DrNicoleTobias/Ray_PaperArtifacts/Review_Material/ITW_Data_Samples/W1_HW1_Summary.png

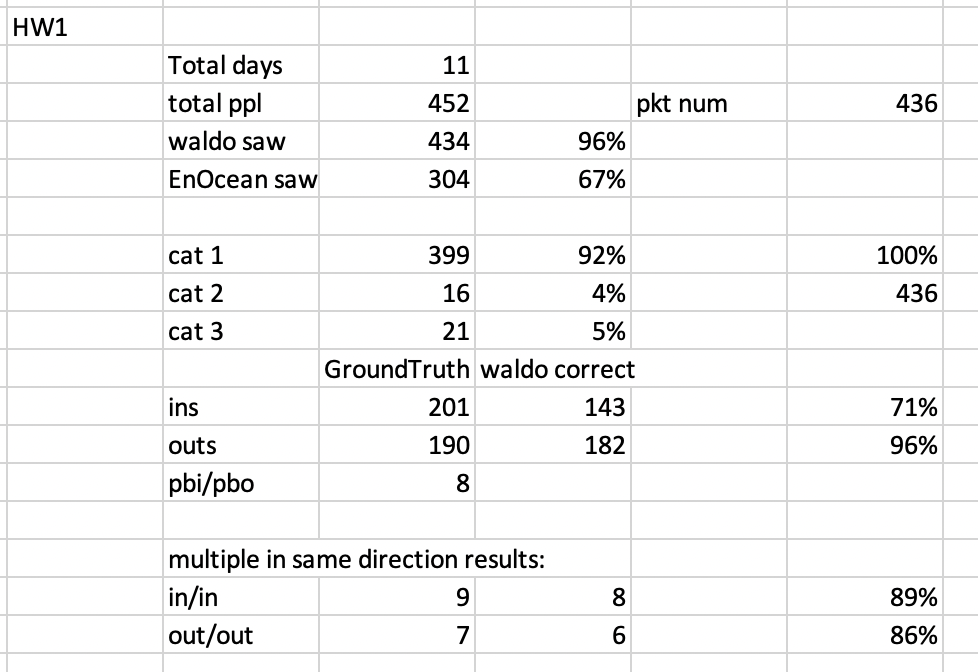
Review_Material/ITW_Data_Samples/W1_HW1_Summary.png
