DrNicoleTobias/Ray_PaperArtifacts/Review_Material/ITW_Data_Samples/W5_GT_All_preHW2_Results.xlsx

Date/Time | Location | GT People Count/event | Category | Ground Truth Label | Description of ground truth if not simple in/out event | Sensor and GT agree | Multiple people same direction results | Waldo/Ray Classifiation | Detect ppl/event | EnOcean Detection
2023-01-10 17:02 | preHW2 | 1 | 1 | out |  | out |  | out | 1 | hit | preHW2
2023-01-10 17:30 | preHW2 | 2 | 2 | in/in | two people come in one after another, about 4 seconds |  | in | in | 1 | hit |  | Total days | 11
2023-01-10 17:46 | preHW2 | 4 | 2 | in/in | four people walk in one after another after another, about 8 seconds |  | in | in | 1 | hit |  | total ppl | 1637 |  | pkt num | 1295
2023-01-10 17:56 | preHW2 | 3 | 2 | in/in | 3 people walk in, one then two came in after together, about 7 seconds |  | in | in | 1 | hit |  | waldo saw | 1316 | 80.39095907%
2023-01-10 18:36 | preHW2 | 1 | 1 | out |  | out |  | out | 1 | hit |  | EnOcean saw | 640 | 39.09590715%
2023-01-10 18:37 | preHW2 | 1 | 1 | in |  | in |  | in | 1 | miss
2023-01-10 18:47 | preHW2 | 1 | 1 | out |  | out |  | out | 1 | hit |  | cat 1 | 1100 | 84.94208494% |  | 99.92277992%
2023-01-10 18:48 | preHW2 | 1 | 1 | in |  | in |  | in | 1 | miss |  | cat 2 | 130 | 10.03861004% |  | 1294
2023-01-10 18:48 | preHW2 | 1 | 1 | out |  | out |  | out | 1 | miss |  | cat 3 | 64 | 4.942084942%
2023-01-11 01:55 | preHW2 | 1 | 1 | out |  | out |  | out | 1 | hit |  |  | GroundTruth | waldo correct
2023-01-11 06:48 | preHW2 | 1 | 1 | in |  | in |  | in | 1 | hit |  | ins | 579 | 560 |  | 96.71848014%
2023-01-11 07:16 | preHW2 | 1 | 1 | in |  |  |  | out | 1 | miss |  | outs | 512 | 476 |  | 92.96875%
2023-01-11 07:19 | preHW2 | 1 | 1 | in |  | in |  | in | 1 | hit |  | pbi/pbo | 9 | 6 |  | 66.66666667%
2023-01-11 07:23 | preHW2 | 1 | 1 | in |  | in |  | in | 1 | hit
2023-01-11 07:34 | preHW2 | 1 | 1 | out |  | out |  | out | 1 | hit |  | multiple in same direction results:
2023-01-11 07:37 | preHW2 | 1 | 1 | in |  | in |  | in | 1 | hit |  | in/in | 65 | 56 |  | 86.15384615%
2023-01-11 07:37 | preHW2 | 1 | 1 | out |  | out |  | out | 1 | miss |  | out/out | 65 | 53 |  | 81.53846154%
2023-01-11 07:44 | preHW2 | 1 | 1 | in |  | in |  | in | 1 | hit
2023-01-11 07:48 | preHW2 | 1 | 1 | pbin | lady comes out of her office off camera |  |  | pbo | 1 | hit
2023-01-11 07:52 | preHW2 | 1 | 1 | in |  | in |  | in | 1 | hit
2023-01-11 07:53 | preHW2 | 1 | 1 | out |  | out |  | out | 1 | miss
2023-01-11 08:27 | preHW2 | 1 | 1 | out |  | out |  | out | 1 | hit
2023-01-11 08:36 | preHW2 | 1 | 1 | out |  | out |  | out | 1 | hit
2023-01-11 08:42 | preHW2 | 1 | 1 | in |  | in |  | in | 1 | hit
2023-01-11 08:43 | preHW2 | 1 | 1 | in |  | in |  | in | 1 | miss
2023-01-11 08:44 | preHW2 | 1 | 1 | in |  | in |  | in | 1 | hit
2023-01-11 08:46 | preHW2 | 1 | 1 | in |  | in |  | in | 1 | miss
2023-01-11 08:46 | preHW2 | 1 | 1 | out |  | out |  | out | 1 | hit
2023-01-11 08:49 | preHW2 | 1 | 1 | in |  | in |  | in | 1 | hit
2023-01-11 08:51 | preHW2 | 1 | 1 | in |  | in |  | in | 1 | hit
2023-01-11 08:57 | preHW2 | 1 | 1 | out |  |  |  | pbi | 1 | hit
2023-01-11 08:57 | preHW2 | 1 | 1 | in |  | in |  | in | 1 | miss
2023-01-11 08:57 | preHW2 | 1 | 1 | out |  | out |  | out | 1 | miss
2023-01-11 09:27 | preHW2 | 1 | 1 | in |  | in |  | in | 1 | hit
2023-01-11 09:32 | preHW2 | 1 | 1 | out |  | out |  | out | 1 | hit
2023-01-11 09:34 | preHW2 | 1 | 1 | out |  | out |  | out | 1 | hit
2023-01-11 09:36 | preHW2 | 1 | 1 | in |  | in |  | in | 1 | hit
2023-01-11 09:44 | preHW2 | 1 | 1 | in |  | in |  | in | 1 | hit
2023-01-11 09:52 | preHW2 | 1 | 1 | out |  | out |  | out | 1 | hit
2023-01-11 09:53 | preHW2 | 1 | 1 | in |  | in |  | in | 1 | miss
2023-01-11 09:54 | preHW2 | 1 | 1 | in |  | in |  | in | 1 | miss
2023-01-11 09:56 | preHW2 | 2 | 3 | out/in | two people walk through in different direction in the same event |  |  | in | 1 | hit
2023-01-11 09:57 | preHW2 | 1 | 1 | out |  |  |  | in | 1 | miss
2023-01-11 10:05 | preHW2 | 1 | 1 | out |  | out |  | out | 1 | hit
2023-01-11 10:06 | preHW2 | 1 | 1 | out |  | out |  | out | 1 | miss
2023-01-11 10:09 | preHW2 | 1 | 1 | in |  | in |  | in | 1 | hit
2023-01-11 10:30 | preHW2 | 1 | 1 | out |  | out |  | out | 1 | hit
2023-01-11 10:31 | preHW2 | 1 | 1 | in |  | in |  | in | 1 | miss
2023-01-11 10:33 | preHW2 | 1 | 1 | in |  | in |  | in | 1 | hit
2023-01-11 10:33 | preHW2 | 1 | 1 | out |  | out |  | out | 1 | miss
2023-01-11 10:34 | preHW2 | 1 | 1 | in |  | in |  | in | 1 | miss
2023-01-11 10:37 | preHW2 | 1 | 1 | out |  | out |  | out | 1 | hit
2023-01-11 10:38 | preHW2 | 2 | 2 | out/out | two people walked out together at the same time |  | out | out | 1 | miss
2023-01-11 10:41 | preHW2 | 1 | 1 | in |  | in |  | in | 1 | hit
2023-01-11 10:43 | preHW2 | 1 | 1 | out |  | out |  | out | 1 | hit
2023-01-11 10:50 | preHW2 | 1 | 1 | in |  | in |  | in | 1 | hit
2023-01-11 10:50 | preHW2 | 1 | 1 | in |  | in |  | in | 1 | miss
2023-01-11 10:51 | preHW2 | 1 | 1 | out |  | out |  | out | 1 | miss
2023-01-11 10:52 | preHW2 | 1 | 1 | out |  | out |  | out | 1 | hit
2023-01-11 10:54 | preHW2 | 1 | 1 | in |  | in |  | in | 1 | miss
2023-01-11 11:05 | preHW2 | 1 | 1 | out |  | out |  | out | 1 | hit
2023-01-11 11:05 | preHW2 | 1 | 1 | in |  | in |  | in | 1 | miss
2023-01-11 11:07 | preHW2 | 2 | 3 | out/in | two people walk through in different direction in the same event |  |  | out | 1 | miss
2023-01-11 11:07 | preHW2 | 1 | 1 | in |  | in |  | in | 1 | miss
2023-01-11 11:07 | preHW2 | 1 | 1 | in |  | in |  | in | 1 | miss
2023-01-11 11:08 | preHW2 | 1 | 1 | out |  | out |  | out | 1 | hit
2023-01-11 11:08 | preHW2 | 2 | 2 | in/in | two people walking in after one another with a few seconds in between, this gt lasted about 7 seconds |  |  | in/in | 2 | miss
2023-01-11 11:09 | preHW2 | 1 | 1 | out |  |  |  | in | 1 | miss
2023-01-11 11:10 | preHW2 | 1 | 1 | in |  | in |  | in | 1 | hit
2023-01-11 11:10 | preHW2 | 1 | 1 | out |  | out |  | out | 1 | miss
2023-01-11 11:11 | preHW2 | 1 | 1 | in |  | in |  | in | 1 | miss
2023-01-11 11:11 | preHW2 | 1 | 1 | in |  | in |  | in | 1 | miss
2023-01-11 11:12 | preHW2 | 1 | 1 | in |  | in |  | in | 1 | hit
2023-01-11 11:14 | preHW2 | 1 | 1 | in |  | in |  | in | 1 | miss
2023-01-11 11:27 | preHW2 | 1 | 1 | out |  | out |  | out | 1 | hit
2023-01-11 11:29 | preHW2 | 1 | 1 | in |  | in |  | in | 1 | miss
2023-01-11 11:54 | preHW2 | 1 | 1 | out |  | out |  | out | 1 | hit
2023-01-11 11:54 | preHW2 | 1 | 1 | out |  | out |  | out | 1 | miss
2023-01-11 11:54 | preHW2 | 9 | 2 | out/out | 9 people walk out, class got out, about 18 seconds of walks |  |  | in/pbi | 2 | miss
2023-01-11 11:56 | preHW2 | 1 | 1 | out |  | out |  | out | 1 | hit
2023-01-11 12:03 | preHW2 | 1 | 1 | in |  | in |  | in | 1 | hit
2023-01-11 12:06 | preHW2 | 1 | 1 | pbin | lady comes in of her office off camera | pb |  | pbi | 1 | hit
2023-01-11 12:07 | preHW2 | 1 | 1 | in |  | in |  | in | 1 | miss
2023-01-11 12:08 | preHW2 | 1 | 1 | out |  | out |  | out | 1 | miss
2023-01-11 12:09 | preHW2 | 1 | 1 | in |  | in |  | in | 1 | hit
2023-01-11 12:09 | preHW2 | 2 | 2 | out/out |  |  | out | out | 1 | miss
2023-01-11 12:12 | preHW2 | 1 | 1 | in |  | in |  | in | 1 | hit
2023-01-11 12:13 | preHW2 | 1 | 1 | in | about 6 seconds | in |  | in | 1 | miss
2023-01-11 12:16 | preHW2 | 1 | 1 | in |  | in |  | in | 1 | hit
2023-01-11 12:24 | preHW2 | 1 | 1 | out |  | out |  | out | 1 | hit
2023-01-11 12:35 | preHW2 | 1 | 1 | out |  | out |  | out | 1 | hit
2023-01-11 12:38 | preHW2 | 1 | 1 | out |  | out |  | out | 1 | hit
2023-01-11 12:39 | preHW2 | 1 | 1 | in |  | in |  | in | 1 | miss
2023-01-11 12:39 | preHW2 | 1 | 1 | in |  | in |  | in | 1 | miss
2023-01-11 12:51 | preHW2 | 1 | 1 | out |  | out |  | out | 1 | hit
2023-01-11 12:52 | preHW2 | 2 | 3 | out/in | some one comes in, the other person is going out,, lingers to talk then continues to go out, about 9 seconds |  |  | in | 1 | miss
2023-01-11 12:52 | preHW2 | 1 | 1 | out |  | out |  | out | 1 | miss
2023-01-11 12:58 | preHW2 | 1 | 1 | in |  | in |  | in | 1 | hit
2023-01-11 12:59 | preHW2 | 1 | 1 | out |  | out |  | out | 1 | miss
2023-01-11 13:00 | preHW2 | 1 | 1 | in |  | in |  | in | 1 | miss
2023-01-11 13:00 | preHW2 | 1 | 1 | in |  | in |  | in | 1 | miss
2023-01-11 13:24 | preHW2 | 2 | 2 | in/in | two people walk in slowly together then linger a bit on the pbin side, about 11 seconds |  | in | in | 1 | hit
2023-01-11 13:30 | preHW2 | 2 | 2 | out/out | two people walk out together |  | out | out | 1 | hit
2023-01-11 13:33 | preHW2 | 1 | 1 | in |  | in |  | in | 1 | hit
2023-01-11 13:38 | preHW2 | 1 | 1 | out |  |  |  | in | 1 | hit
2023-01-11 13:40 | preHW2 | 3 | 2 | in/in | one person walks in followed by two walking in together |  | in | in | 1 | hit
2023-01-11 13:47 | preHW2 | 1 | 1 | out |  | out |  | out | 1 | hit
2023-01-11 13:54 | preHW2 | 1 | 1 | in |  | in |  | in | 1 | hit
2023-01-11 13:54 | preHW2 | 1 | 3 | uturn | person starts to go out then switches back in, hard to tell if she crossed the sensor |  |  | in | 1 | miss
2023-01-11 14:03 | preHW2 | 1 | 1 | out |  | out |  | out | 1 | hit
2023-01-11 14:05 | preHW2 | 1 | 1 | in |  | in |  | in | 1 | hit
2023-01-11 14:06 | preHW2 | 1 | 1 | in |  | in |  | in | 1 | miss
2023-01-11 14:08 | preHW2 | 1 | 1 | out |  |  |  | in | 1 | hit
2023-01-11 14:08 | preHW2 | 2 | 3 | out/in | two people walk out in opposite directions |  |  | out | 1 | miss
2023-01-11 14:11 | preHW2 | 3 | 2 | in/in | three, one then two people walkin in with a couple of seconds between |  | in | in | 1 | hit
2023-01-11 14:12 | preHW2 | 1 | 1 | in |  | in |  | in | 1 | miss
2023-01-11 14:14 | preHW2 | 1 | 1 | out |  | out |  | out | 1 | hit
2023-01-11 14:16 | preHW2 | 1 | 1 | in |  | in |  | in | 1 | miss
2023-01-11 14:17 | preHW2 | 2 | 2 | out/out | two people walk out side by side |  | out | out | 1 | hit
2023-01-11 14:20 | preHW2 | 1 | 1 | out |  | out |  | out | 1 | hit
2023-01-11 14:21 | preHW2 | 2 | 2 | in/in | two people walk in side by side |  | in | in | 1 | miss
2023-01-11 14:21 | preHW2 | 1 | 1 | out |  | out |  | out | 1 | miss
2023-01-11 14:22 | preHW2 | 1 | 1 | in |  | in |  | in | 1 | hit
2023-01-11 14:24 | preHW2 | 1 | 1 | in |  | in |  | in | 1 | miss
2023-01-11 14:26 | preHW2 | 1 | 1 | out |  | out |  | out | 1 | hit
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
2023-01-12 10:53 | preHW2 | 1 | 1 | in |  | in |  | in | 1 | miss
2023-01-12 10:54 | preHW2 | 1 | 1 | out |  | out |  | out | 1 | hit
2023-01-12 10:55 | preHW2 | 1 | 1 | in |  | in |  | in | 1 | miss
2023-01-12 11:34 | preHW2 | 1 | 1 | out |  | out |  | out | 1 | hit
2023-01-12 11:37 | preHW2 | 23 | 3 | out/out/linger | twenty-three students exit out, kind of linger, finish the exit, about 47 seconds |  |  | out/in/in/out/in | 5 | hit
2023-01-12 11:39 | preHW2 | 23 | 2 | in/in | twenty-three students exit in, about 25 seconds |  |  | in/in/in/pbout | 4 | miss
2023-01-12 11:41 | preHW2 | 1 | 1 | in |  | in |  | in | 1 | hit
2023-01-12 11:45 | preHW2 | 1 | 1 | out |  | out |  | out | 1 | hit
2023-01-12 11:45 | preHW2 | 1 | 1 | out |  | out |  | out | 1 | miss
2023-01-12 11:48 | preHW2 | 1 | 1 | out |  | out |  | out | 1 | hit
2023-01-12 11:50 | preHW2 | 1 | 1 | in |  | in |  | in | 1 | hit
2023-01-12 11:51 | preHW2 | 2 | 2 | in/in | two people walk in side by side, about 2 seconds |  | in | in | 1 | miss
2023-01-12 11:53 | preHW2 | 1 | 1 | out |  | out |  | out | 1 | hit
2023-01-12 11:54 | preHW2 | 1 | 1 | in |  | in |  | in | 1 | miss
2023-01-12 12:00 | preHW2 | 2 | 2 | out/out | two people back to back |  | out | out | 1 | hit
2023-01-12 12:00 | preHW2 | 1 | 1 | out | will likely get lumped in with the last one |  |  | pbi | 1 | miss
2023-01-12 12:01 | preHW2 | 1 | 3 | uturn | about 7 seconds |  |  | pbin/in | 1 | miss
2023-01-12 12:02 | preHW2 | 2 | 3 | out/in | two people walk in back to back, about 3 seconds then two people cross under the sensor in different directions, about 5 seconds |  |  | out/pbi | 2 | hit
2023-01-12 12:05 | preHW2 | 1 | 1 | in |  | in |  | in | 1 | hit
2023-01-12 12:07 | preHW2 | 1 | 1 | in |  | in |  | in | 1 | hit
2023-01-12 12:08 | preHW2 | 1 | 1 | out |  | out |  | out | 1 | miss
2023-01-12 12:08 | preHW2 | 1 | 1 | out |  | out |  | out | 1 | miss
2023-01-12 12:09 | preHW2 | 2 | 2 | out/out | two people walk out back to back, about 4 seconds |  | out | out | 1 | hit
2023-01-12 12:11 | preHW2 | 1 | 1 | in |  | in |  | in | 1 | miss
2023-01-12 12:12 | preHW2 | 1 | 1 | out |  | out |  | out | 1 | hit
2023-01-12 12:12 | preHW2 | 2 | 2 | in/in | two people walk in back to back, about 5 seconds |  | in | in | 1 | miss
2023-01-12 12:12 | preHW2 | 1 | 1 | pbout | guy walks by wall, maybe no event |  |  | pbi | 1 | miss
2023-01-12 12:15 | preHW2 | 1 | 1 | in |  | in |  | in | 1 | hit
2023-01-12 12:15 | preHW2 | 1 | 1 | in |  | in |  | in | 1 | miss
2023-01-12 12:16 | preHW2 | 1 | 1 | in |  | in |  | in | 1 | miss
2023-01-12 12:16 | preHW2 | 1 | 1 | out |  | out |  | out | 1 | miss
2023-01-12 12:17 | preHW2 | 1 | 1 | in |  | in |  | in | 1 | miss
2023-01-12 12:17 | preHW2 | 1 | 1 | out |  | out |  | out | 1 | miss
2023-01-12 12:17 | preHW2 | 1 | 1 | out |  | out |  | out | 1 | hit
2023-01-12 12:19 | preHW2 | 1 | 1 | in |  | in |  | in | 1 | miss
2023-01-12 12:21 | preHW2 | 2 | 2 | in/in | two people walk in back to back, about 4 seconds |  | in | in | 1 | hit
2023-01-12 12:22 | preHW2 | 2 | 2 | in/in | two people walk in back to back, about 5 seconds |  | in | in | 1 | miss
2023-01-12 12:22 | preHW2 | 1 | 1 | out |  | out |  | out | 1 | miss
2023-01-12 12:22 | preHW2 | 1 | 1 | out |  | out |  | out | 1 | miss
2023-01-12 12:23 | preHW2 | 1 | 1 | out |  | out |  | out | 1 | miss
2023-01-12 12:24 | preHW2 | 1 | 1 | in |  | in |  | in | 1 | hit
2023-01-12 12:28 | preHW2 | 1 | 1 | in |  | in |  | in | 1 | hit
2023-01-12 12:30 | preHW2 | 1 | 1 | in |  | in |  | in | 1 | hit
2023-01-12 12:30 | preHW2 | 1 | 1 | out |  |  |  | in | 1 | miss
2023-01-12 12:31 | preHW2 | 1 | 1 | in |  | in |  | in | 1 | miss
2023-01-12 12:32 | preHW2 | 1 | 1 | in |  | in |  | in | 1 | hit
2023-01-12 12:33 | preHW2 | 1 | 1 | out |  | out |  | out | 1 | miss
2023-01-12 12:36 | preHW2 | 1 | 1 | pbin |  | pb |  | pbi | 1 | hit
2023-01-12 12:36 | preHW2 | 1 | 1 | out |  | out |  | out | 1 | miss
2023-01-12 12:37 | preHW2 | 1 | 1 | in |  | in |  | in | 1 | miss
2023-01-12 12:38 | preHW2 | 1 | 1 | in |  | in |  | in | 1 | hit
2023-01-12 12:38 | preHW2 | 1 | 1 | in |  | in |  | in | 1 | miss
2023-01-12 12:39 | preHW2 | 1 | 1 | out |  | out |  | out | 1 | miss
2023-01-12 12:41 | preHW2 | 1 | 1 | out |  | out |  | out | 1 | hit
2023-01-12 12:43 | preHW2 | 1 | 1 | in |  | in |  | in | 1 | hit
2023-01-12 13:15 | preHW2 | 1 | 1 | out |  |  |  | in | 1 | hit
2023-01-12 13:16 | preHW2 | 1 | 1 | out |  | out |  | out | 1 | miss
2023-01-12 13:17 | preHW2 | 1 | 1 | in |  | in |  | in | 1 | hit
2023-01-12 13:18 | preHW2 | 1 | 1 | out |  | out |  | out | 1 | miss
2023-01-12 13:19 | preHW2 | 3 | 3 | out/in | three peopole out, in, in, about 6 seconds |  |  | in | 1 | hit
2023-01-12 13:23 | preHW2 | 1 | 1 | in |  | in |  | in | 1 | hit
2023-01-12 13:31 | preHW2 | 2 | 2 | out/out | two people walk out back to back, about 5 seconds |  | out | out | 1 | hit
2023-01-12 13:31 | preHW2 | 3 | 2 | out/out | three people walk in back to back, about 5 seconds |  | out | out | 1 | miss
2023-01-12 13:32 | preHW2 | 1 | 1 | out |  | out |  | out | 1 | miss
2023-01-12 13:32 | preHW2 | 3 | 3 | in/out | three people in, out, out, in different directions about 5 seconds |  |  | out | 1 | miss
2023-01-12 13:32 | preHW2 | 1 | 1 | in |  | in |  | in | 1 | miss
2023-01-12 13:43 | preHW2 | 1 | 1 | in |  | in |  | in | 1 | hit
2023-01-12 13:43 | preHW2 | 6 | 3 | out/in | six people walk under the sensor in different directions, about 10 seconds |  |  | in | 1 | miss
2023-01-12 13:44 | preHW2 | 2 | 2 | in/in | two people walk in side by side, about 2 seconds |  | in | in | 1 | hit
2023-01-12 13:45 | preHW2 | 1 | 1 | in |  | in |  | in | 1 | miss
2023-01-12 13:46 | preHW2 | 1 | 1 | in |  | in |  | in | 1 | miss
2023-01-12 13:48 | preHW2 | 2 | 2 | in/in | two people walk in back to back, about 3 seconds |  | in | in | 1 | hit
2023-01-12 13:49 | preHW2 | 3 | 2 | in/in | three people walk in back to back, about 5 seconds |  | in | in | 1 | miss
2023-01-12 13:51 | preHW2 | 1 | 1 | out |  | out |  | out | 1 | hit
2023-01-12 13:51 | preHW2 | 1 | 1 | out |  | out |  | out | 1 | miss
2023-01-12 13:51 | preHW2 | 1 | 1 | in |  | in |  | in | 1 | miss
2023-01-12 13:52 | preHW2 | 1 | 1 | in |  | in |  | in | 1 | miss
2023-01-12 13:55 | preHW2 | 1 | 1 | out |  | out |  | out | 1 | hit
2023-01-12 13:59 | preHW2 | 2 | 3 | out/in |  |  |  | pbin/in | 2 | hit
2023-01-12 14:48 | preHW2 | 1 | 1 | out |  | out |  | out | 1 | hit
2023-01-12 14:49 | preHW2 | 2 | 3 | in/out |  |  |  | in | 1 | miss
2023-01-12 14:50 | preHW2 | 1 | 1 | out |  | out |  | out | 1 | hit
2023-01-12 14:52 | preHW2 | 1 | 1 | in |  | in |  | in | 1 | hit
2023-01-12 15:02 | preHW2 | 3 | 2 | out/out | three people walk out back to back, about 6 seconds |  | out | out | 1 | hit
2023-01-12 15:02 | preHW2 | 2 | 2 | out/out | two people walk out back to back, about 3 seconds |  | out | out | 1 | miss
2023-01-12 15:04 | preHW2 | 1 | 1 | out |  | out |  | out | 1 | hit
2023-01-12 15:04 | preHW2 | 2 | 2 | in/in | two people walk in side by side, about 2 seconds |  | in | in | 1 | miss
2023-01-12 15:06 | preHW2 | 1 | 1 | in |  | in |  | in | 1 | hit
2023-01-12 15:13 | preHW2 | 1 | 1 | out |  | out |  | out | 1 | hit
2023-01-12 15:15 | preHW2 | 1 | 1 | out |  | out |  | out | 1 | miss
2023-01-12 15:15 | preHW2 | 1 | 1 | in |  | in |  | in | 1 | hit
2023-01-12 15:29 | preHW2 | 1 | 1 | out |  | out |  | out | 1 | hit
2023-01-12 15:32 | preHW2 | 1 | 1 | in |  | in |  | in | 1 | hit
2023-01-12 16:25 | preHW2 | 1 | 1 | in |  | in |  | in | 1 | hit
2023-01-12 16:41 | preHW2 | 1 | 3 | in/linger/curiosity | guy stops to look at the sensor, about 7 seconds |  |  | in | 1 | hit
2023-01-12 16:49 | preHW2 | 1 | 1 | out |  | out |  | out | 1 | hit
2023-01-12 16:57 | preHW2 | 1 | 1 | out |  | out |  | out | 1 | hit
2023-01-12 19:12 | preHW2 | 1 | 1 | out |  | out |  | out | 1 | hit
2023-01-12 19:13 | preHW2 | 1 | 1 | in |  | in |  | in | 1 | miss
2023-01-12 22:40 | preHW2 | 1 | 1 | in | janitor with trash can | in |  | in | 1 | hit
2023-01-12 22:48 | preHW2 | 1 | 1 | out | janitor with trash can | out |  | out | 1 | hit
2023-01-12 23:57 | preHW2 | 1 | 1 | in | janitor with cart | in |  | in | 1 | hit
2023-01-12 23:59 | preHW2 | 1 | 1 | out | janitor with cart | out |  | out | 1 | hit
2023-01-13 06:47 | preHW2 | 1 | 1 | in |  | in |  | in | 1 | hit
2023-01-13 06:59 | preHW2 | 1 | 1 | out |  | out |  | out | 1 | hit
2023-01-13 07:02 | preHW2 | 1 | 1 | in |  | in |  | in | 1 | hit
2023-01-13 07:46 | preHW2 | 1 | 1 | out |  | out |  | out | 1 | hit
2023-01-13 07:47 | preHW2 | 1 | 1 | pbout | shadow from off camera view | pb |  | pbo | 1 | miss
2023-01-13 08:41 | preHW2 | 1 | 1 | out |  | out |  | out | 1 | hit
2023-01-13 08:47 | preHW2 | 1 | 1 | in |  | in |  | in | 1 | hit
2023-01-13 08:58 | preHW2 | 1 | 1 | out |  | out |  | out | 1 | hit
2023-01-13 09:00 | preHW2 | 2 | 2 | in/in | two people walk in back to back, about 4 seconds |  | in | in | 1 | miss
2023-01-13 09:02 | preHW2 | 1 | 1 | in |  | in |  | in | 1 | hit
2023-01-13 09:06 | preHW2 | 1 | 1 | in |  | in |  | in | 1 | hit
2023-01-13 09:07 | preHW2 | 1 | 1 | in |  | in |  | in | 1 | miss
2023-01-13 09:07 | preHW2 | 1 | 1 | out |  |  |  | in | 1 | miss
2023-01-13 09:49 | preHW2 | 1 | 1 | in |  | in |  | in | 1 | hit
2023-01-13 09:53 | preHW2 | 1 | 1 | in |  | in |  | in | 1 | hit
2023-01-13 09:56 | preHW2 | 1 | 1 | out |  | out |  | out | 1 | hit
2023-01-13 09:58 | preHW2 | 1 | 1 | in |  | in |  | in | 1 | hit
2023-01-13 10:03 | preHW2 | 2 | 2 | in/in | two people walk in side by side, about 6 seconds |  |  | in/pbo | 2 | hit
2023-01-13 10:04 | preHW2 | 2 | 2 | out/out | two people walk iout back to back, about 5 seconds |  |  | in | 1 | miss
2023-01-13 10:05 | preHW2 | 1 | 1 | in |  | in |  | in | 1 | miss
2023-01-13 10:08 | preHW2 | 1 | 1 | in |  | in |  | in | 1 | hit
2023-01-13 10:12 | preHW2 | 1 | 1 | in |  | in |  | in | 1 | hit
2023-01-13 10:37 | preHW2 | 1 | 1 | out |  | out |  | out | 1 | hit
2023-01-13 10:39 | preHW2 | 1 | 1 | in |  | in |  | in | 1 | miss
2023-01-13 10:51 | preHW2 | 1 | 1 | in |  | in |  | in | 1 | hit
2023-01-13 10:51 | preHW2 | 1 | 1 | out |  | out |  | out | 1 | miss
2023-01-13 10:55 | preHW2 | 1 | 1 | out |  | out |  | out | 1 | hit
2023-01-13 10:57 | preHW2 | 1 | 1 | out |  |  |  | pbo | 1 | miss
2023-01-13 10:57 | preHW2 | 2 | 2 | out/out | two people walk in back to back several seconds apart, about 7 seconds |  | out | out | 1 | miss
2023-01-13 10:57 | preHW2 | 1 | 1 | out |  |  |  | in | 1 | hit
2023-01-13 10:58 | preHW2 | 1 | 1 | in |  | in |  | in | 1 | miss
2023-01-13 10:58 | preHW2 | 1 | 1 | in |  | in |  | in | 1 | miss
2023-01-13 10:59 | preHW2 | 1 | 1 | out |  | out |  | out | 1 | miss
2023-01-13 11:03 | preHW2 | 1 | 1 | in |  | in |  | in | 1 | hit
2023-01-13 11:03 | preHW2 | 1 | 1 | in |  | in |  | in | 1 | miss
2023-01-13 11:03 | preHW2 | 3 | 3 | in/out | three people in, in, out under the sensor in about 5 seconds |  |  | in | 1 | miss
2023-01-13 11:03 | preHW2 | 1 | 1 | in |  | in |  | in | 1 | miss
2023-01-13 11:06 | preHW2 | 1 | 1 | in |  | in |  | in | 1 | hit
2023-01-13 11:08 | preHW2 | 1 | 1 | in |  | in |  | in | 1 | miss
2023-01-13 11:08 | preHW2 | 1 | 1 | in |  | in |  | in | 1 | miss
2023-01-13 11:10 | preHW2 | 1 | 1 | out |  | out |  | out | 1 | hit
2023-01-13 11:13 | preHW2 | 1 | 1 | in |  | in |  | in | 1 | hit
2023-01-13 11:59 | preHW2 | 2 | 2 | out/out | two people walk out back to back, about 6 seconds |  | out | out | 1 | hit
2023-01-13 11:59 | preHW2 | 4 | 3 | out/out/linger | four people walk out and linger about 11 seconds |  |  | out/out | 2 | miss
2023-01-13 11:59 | preHW2 | 1 | 1 | out |  | out |  | out | 1 | miss
2023-01-13 11:59 | preHW2 | 2 | 2 | out/out | two people walk out back to back, about 4 seconds |  | out | out | 1 | miss
2023-01-13 12:00 | preHW2 | 1 | 1 | out |  | out |  | out | 1 | miss
2023-01-13 12:00 | preHW2 | 1 | 1 | out |  | out |  | out | 1 | miss
2023-01-13 12:02 | preHW2 | 1 | 1 | out |  | out |  | out | 1 | hit
2023-01-13 12:18 | preHW2 | 1 | 1 | out |  | out |  | out | 1 | hit
2023-01-13 12:19 | preHW2 | 1 | 1 | out |  | out |  | out | 1 | miss
2023-01-13 12:20 | preHW2 | 1 | 1 | in |  | in |  | in | 1 | miss
2023-01-13 12:21 | preHW2 | 1 | 1 | in |  | in |  | in | 1 | hit
2023-01-13 12:22 | preHW2 | 2 | 2 | out/out | two people walk out side by side, about 4 seconds |  | out | out | 1 | miss
2023-01-13 12:28 | preHW2 | 1 | 1 | out |  | out |  | out | 1 | hit
2023-01-13 12:30 | preHW2 | 1 | 1 | in |  | in |  | in | 1 | hit
2023-01-13 12:46 | preHW2 | 1 | 1 | in |  | in |  | in | 1 | hit
2023-01-13 13:02 | preHW2 | 1 | 1 | in |  | in |  | in | 1 | hit
2023-01-13 13:47 | preHW2 | 1 | 1 | in |  | in |  | in | 1 | hit
2023-01-13 13:47 | preHW2 | 1 | 1 | out |  | out |  | out | 1 | miss
2023-01-13 13:47 | preHW2 | 1 | 1 | in |  | in |  | in | 1 | miss
2023-01-13 13:49 | preHW2 | 1 | 1 | out |  | out |  | out | 1 | miss
2023-01-13 13:57 | preHW2 | 1 | 1 | out |  | out |  | out | 1 | hit
2023-01-13 14:00 | preHW2 | 1 | 1 | out |  | out |  | out | 1 | hit
2023-01-13 14:00 | preHW2 | 1 | 1 | in |  | in |  | in | 1 | miss
2023-01-13 14:02 | preHW2 | 1 | 1 | out |  | out |  | out | 1 | hit
2023-01-13 14:03 | preHW2 | 1 | 1 | in |  | in |  | in | 1 | miss
2023-01-13 14:31 | preHW2 | 1 | 1 | in |  | in |  | in | 1 | hit
2023-01-13 14:41 | preHW2 | 1 | 1 | out |  | out |  | out | 1 | hit
2023-01-13 14:44 | preHW2 | 1 | 1 | in |  | in |  | in | 1 | hit
2023-01-13 14:45 | preHW2 | 1 | 1 | out |  | out |  | out | 1 | miss
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
